CAST2022/CAST/Hardware/M3 Pan Head 6mm.SLDPRT

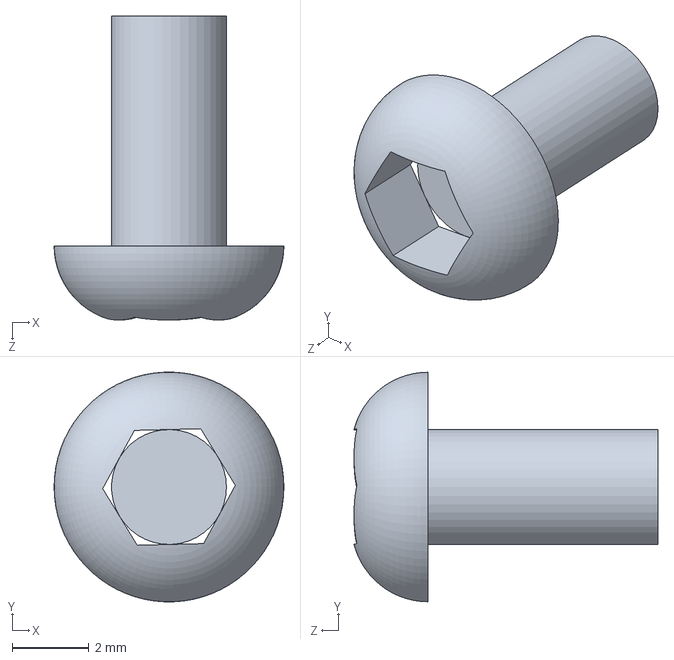
[picture p14: CAD file, 2021-12-28]
Hardware/M3 Pan Head 6mm.SLDPRT
6.00 x 5.99 x 7.94 mm
