CAST2022/CAST/Hardware/SOLIDWORKSComposer/encoderBracketV2.SLDPRT

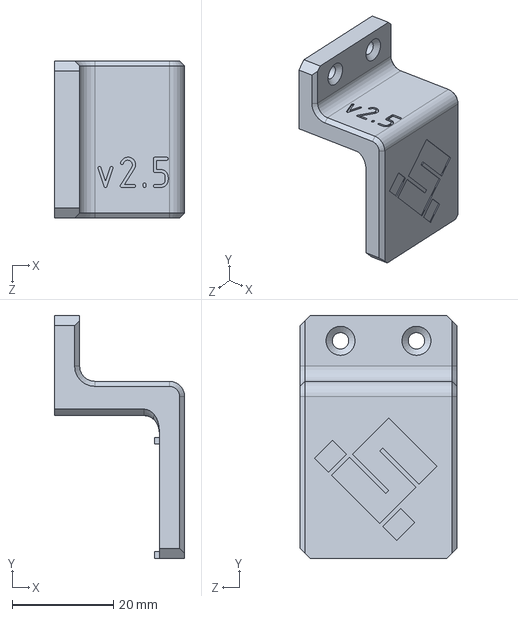
[picture p15: CAD file, 2021-12-27]
Hardware/SOLIDWORKSComposer/encoderBracketV2.SLDPRT
25.8 x 48.0 x 31.0 mm
