CAST2022/CAST/Hardware/SC8LUU Double Bearing Mount.SLDPRT

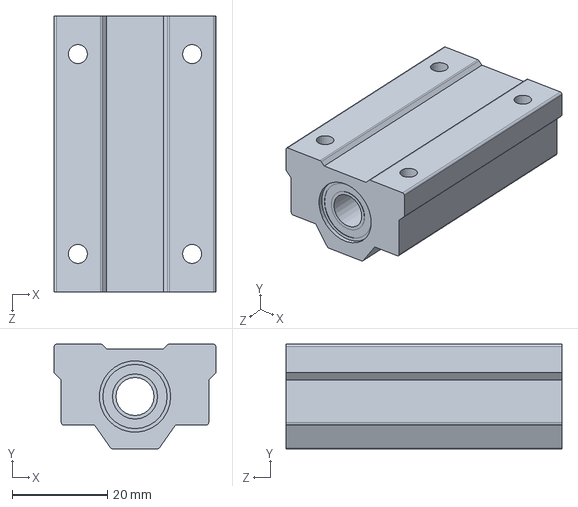
[picture p16: CAD file, 2021-12-28]
Hardware/SC8LUU Double Bearing Mount.SLDPRT
34.0 x 22.0 x 58.0 mm
