CAST2022/CAST/Hardware/SOLIDWORKSComposer/batMount v2.3.SLDPRT

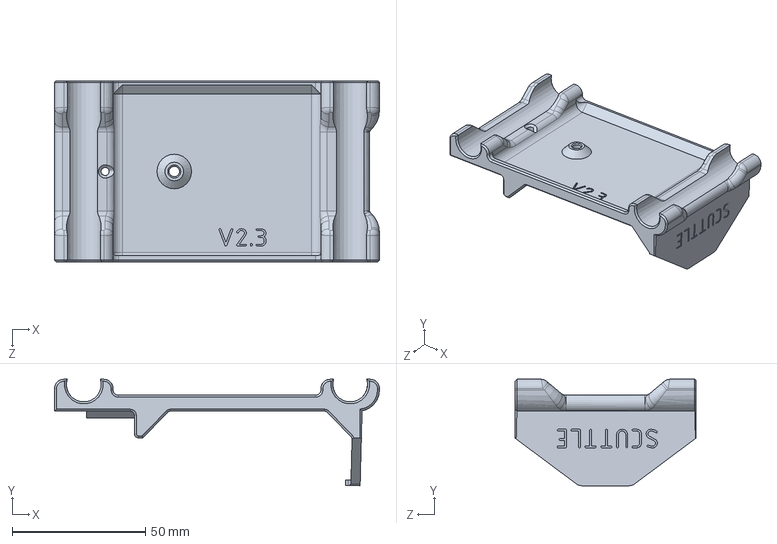
[picture p17: CAD file, 2021-12-27]
Hardware/SOLIDWORKSComposer/batMount v2.3.SLDPRT
122.0 x 40.0 x 68.0 mm
