CAST2022/CAST/Hardware/Nema 17 Mount.SLDPRT

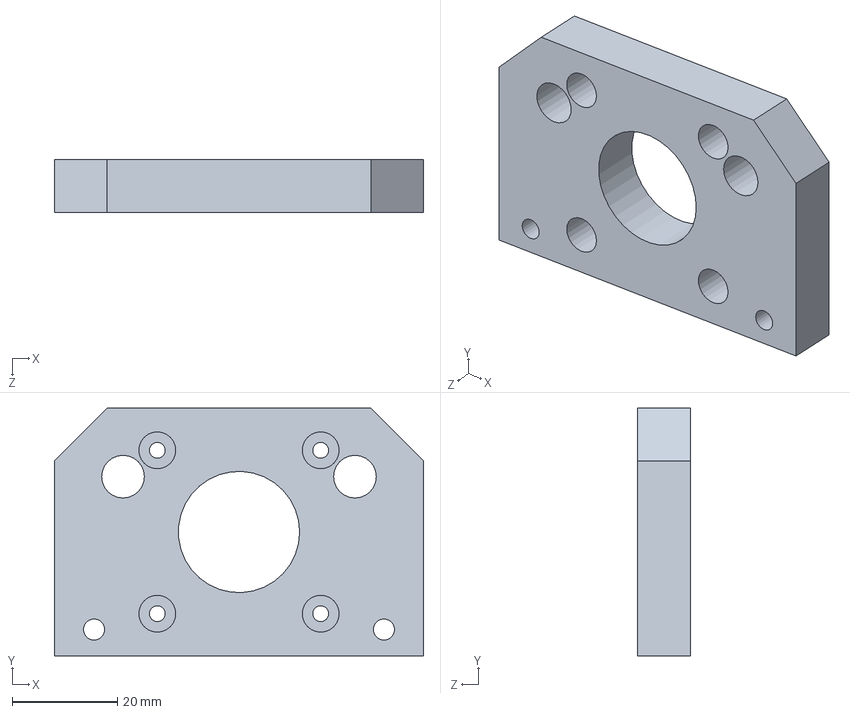
[picture p18: CAD file, 2021-12-28]
Hardware/Nema 17 Mount.SLDPRT
70.0 x 47.0 x 10.0 mm
