CAST2022/CAST/Hardware/SOLIDWORKSComposer/casterCarrier.SLDPRT

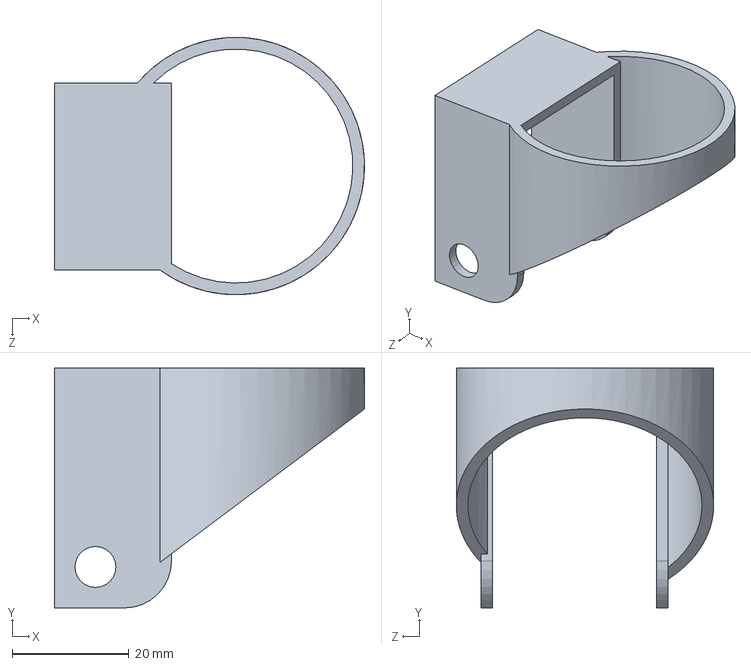
[picture p19: CAD file, 2021-12-27]
Hardware/SOLIDWORKSComposer/casterCarrier.SLDPRT
53.0 x 41.0 x 44.0 mm
