CAST2022/CAST/Hardware/12.17 by 3.54 in cover.SLDPRT

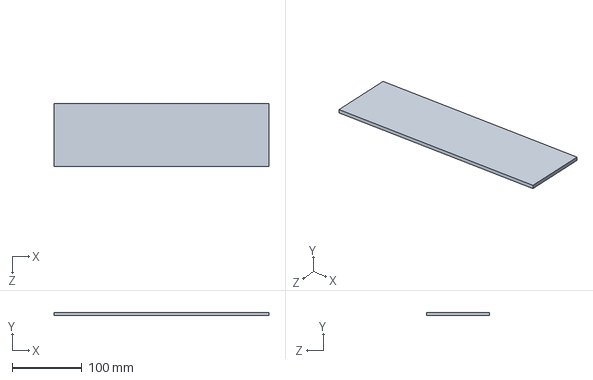
[picture p20: CAD file, 2021-12-28]
Hardware/12.17 by 3.54 in cover.SLDPRT
309.0 x 4.76 x 89.9 mm
