CAST2022/CAST/Hardware/SOLIDWORKSComposer/motor v1.sldprt

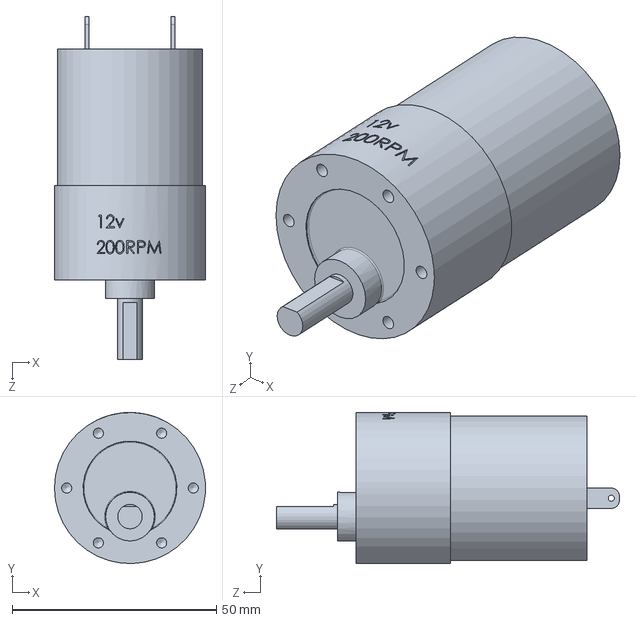
[picture p21: CAD file, 2021-12-27]
Hardware/SOLIDWORKSComposer/motor v1.sldprt
37.0 x 37.0 x 84.0 mm
