CAST2022/CAST/Hardware/SOLIDWORKSComposer/endCap.SLDPRT

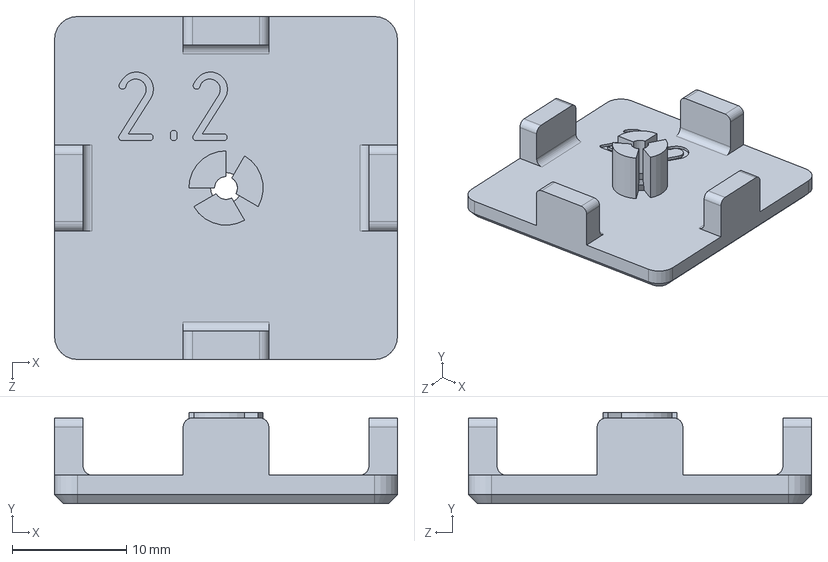
[picture p22: CAD file, 2021-12-27]
Hardware/SOLIDWORKSComposer/endCap.SLDPRT
30.0 x 8.00 x 30.0 mm
