CAST2022/CAST/Hardware/46.31 by 7.28 in cover.SLDPRT

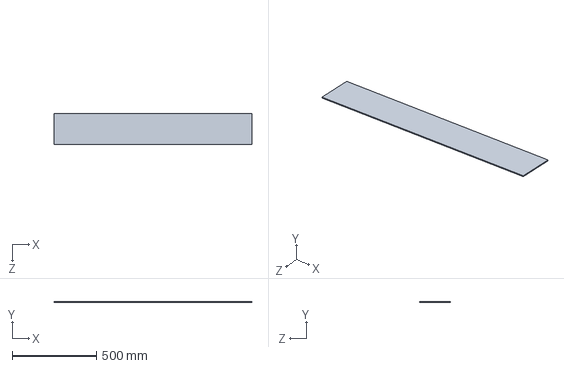
[picture p23: CAD file, 2021-12-28]
Hardware/46.31 by 7.28 in cover.SLDPRT
1176.3 x 4.76 x 184.8 mm
