CAST2022/CAST/Hardware/12.17 by 6 in cover.SLDPRT

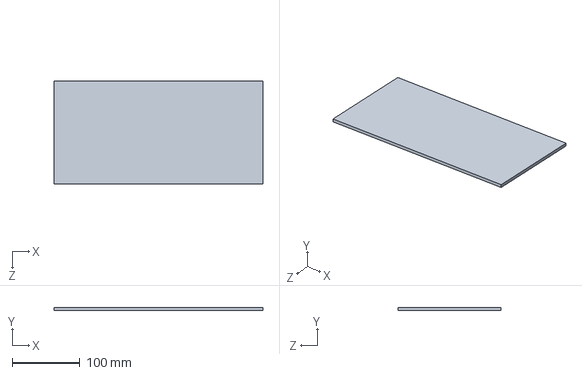
[picture p24: CAD file, 2021-12-28]
Hardware/12.17 by 6 in cover.SLDPRT
309.0 x 4.76 x 152.4 mm
