CAST2022/CAST/Hardware/SOLIDWORKSComposer/BeagleMount V2.SLDPRT

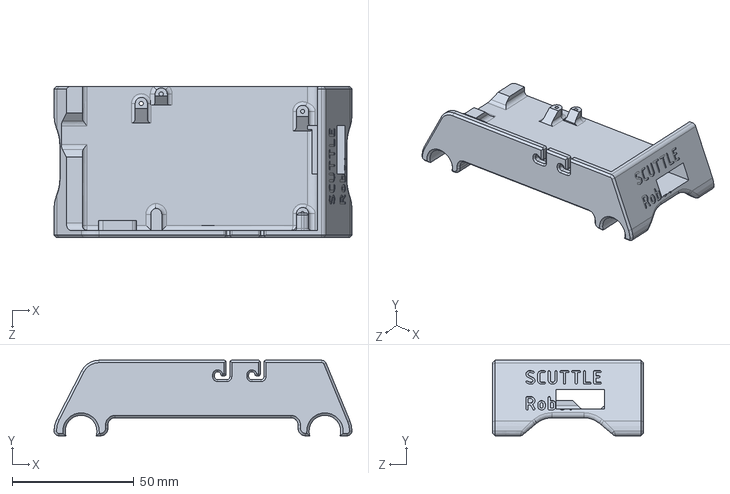
[picture p25: CAD file, 2021-12-27]
Hardware/SOLIDWORKSComposer/BeagleMount V2.SLDPRT
122.2 x 31.0 x 62.0 mm
