CAST2022/CAST/Hardware/RPLiDAR S2.SLDPRT

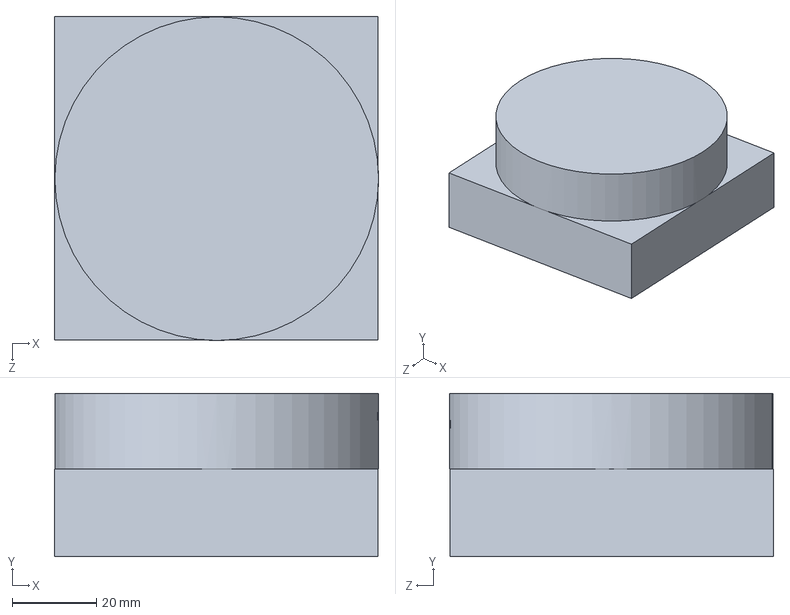
[picture p26: CAD file, 2021-12-28]
Hardware/RPLiDAR S2.SLDPRT
77.1 x 38.8 x 77.1 mm
