CAST2022/CAST/Hardware/SOLIDWORKSComposer/batPCB.SLDPRT

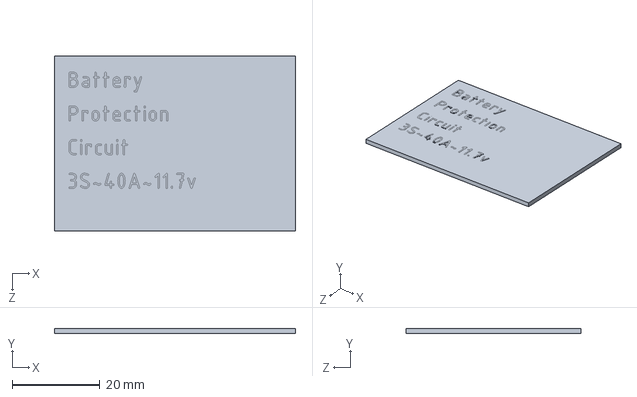
[picture p27: CAD file, 2021-12-27]
Hardware/SOLIDWORKSComposer/batPCB.SLDPRT
55.0 x 1.25 x 40.0 mm
