CAST2022/CAST/Hardware/SOLIDWORKSComposer/batPanel.SLDPRT

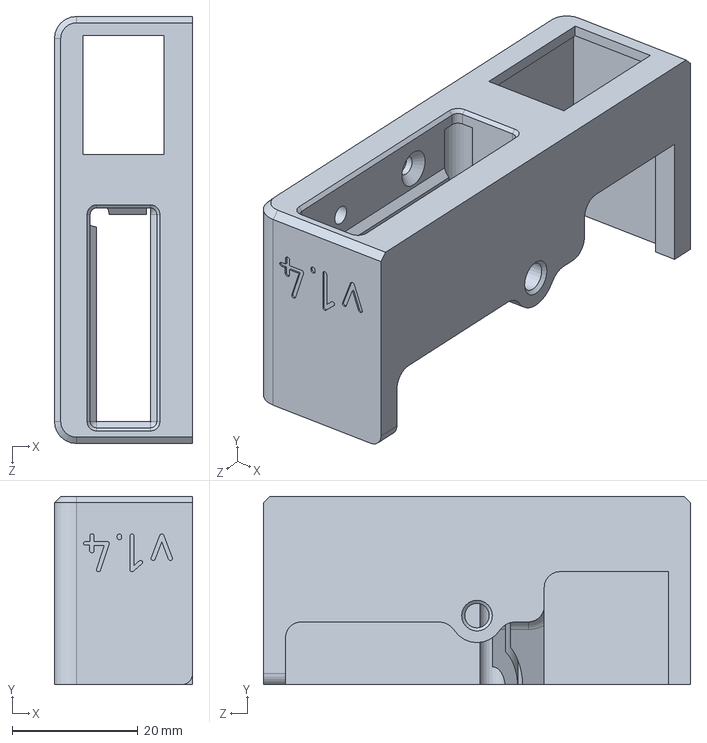
[picture p28: CAD file, 2021-12-27]
Hardware/SOLIDWORKSComposer/batPanel.SLDPRT
22.0 x 30.0 x 68.0 mm
