CAST2022/CAST/Hardware/UV LED PCB.SLDPRT

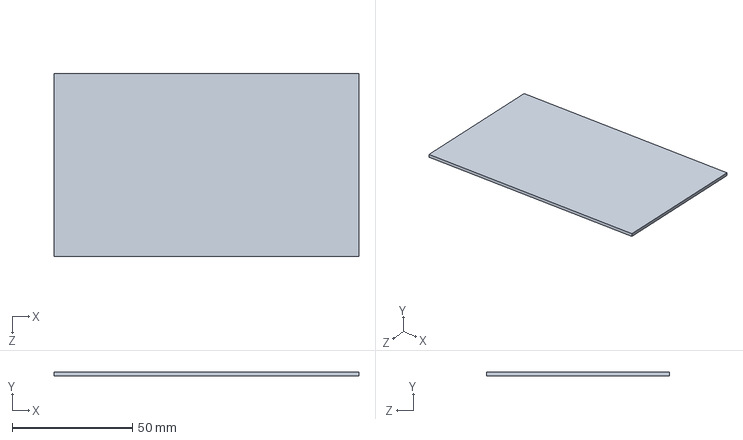
[picture p29: CAD file, 2021-12-28]
Hardware/UV LED PCB.SLDPRT
127.0 x 1.59 x 76.2 mm
