CAST2022/CAST/Hardware/8mm x 721mm Rod.SLDPRT

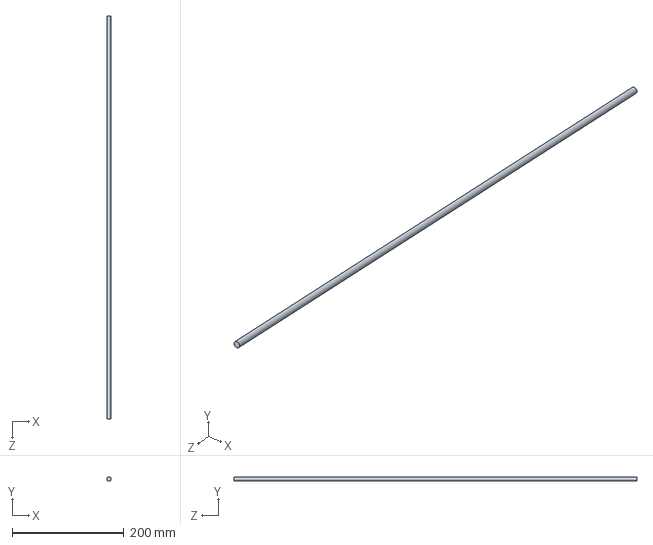
[picture p30: CAD file, 2021-12-28]
Hardware/8mm x 721mm Rod.SLDPRT
8.00 x 8.00 x 721.0 mm
