CAST2022/CAST/Hardware/SOLIDWORKSComposer/casterPlate.SLDPRT

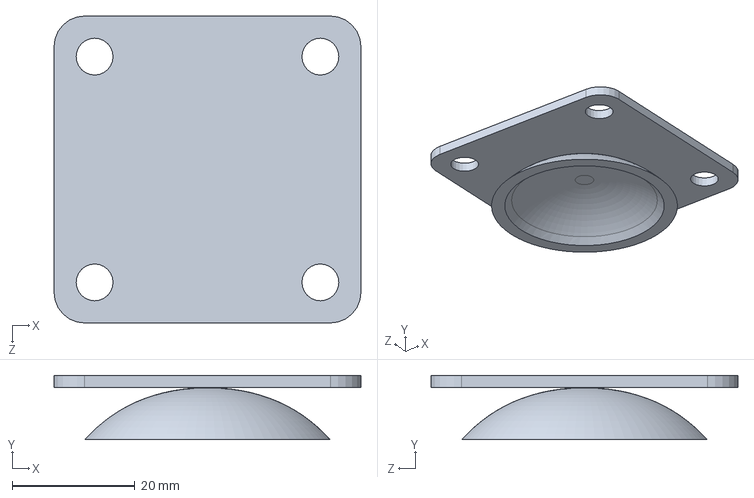
[picture p31: CAD file, 2021-12-27]
Hardware/SOLIDWORKSComposer/casterPlate.SLDPRT
50.0 x 10.5 x 50.0 mm
