CAST2022/CAST/Hardware/SOLIDWORKSComposer/casterWheel.SLDPRT

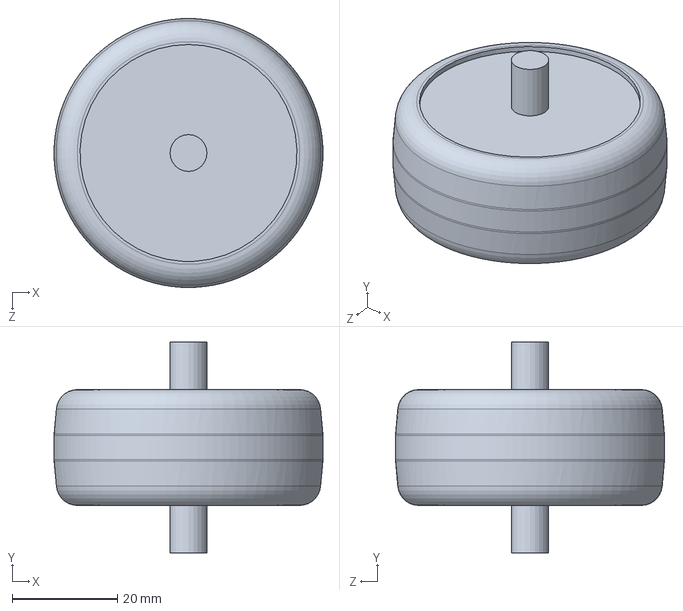
[picture p32: CAD file, 2021-12-27]
Hardware/SOLIDWORKSComposer/casterWheel.SLDPRT
51.1 x 40.0 x 51.1 mm
