CAST2022/CAST/Hardware/37.65 by 7.28 in cover.SLDPRT

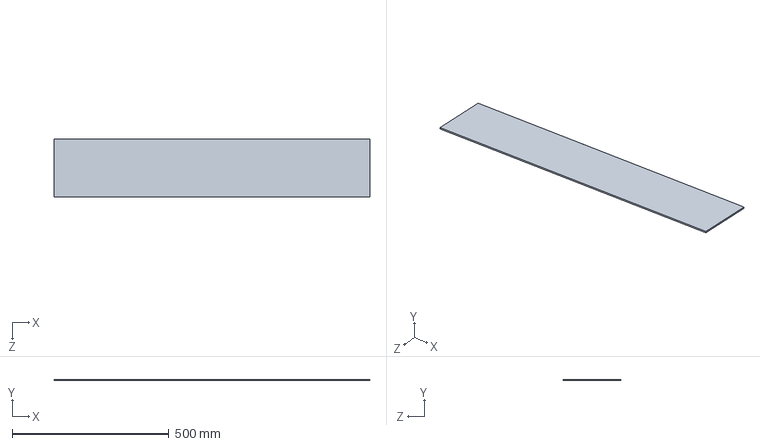
[picture p33: CAD file, 2021-12-28]
Hardware/37.65 by 7.28 in cover.SLDPRT
1007.1 x 4.76 x 184.8 mm
