CAST2022/CAST/Hardware/Plate to support RPLiDAR.SLDPRT

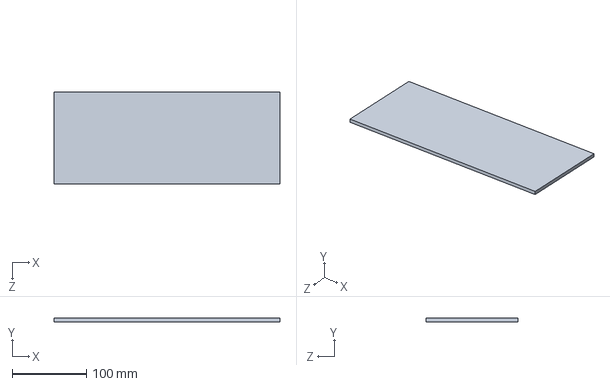
[picture p34: CAD file, 2021-12-28]
Hardware/Plate to support RPLiDAR.SLDPRT
304.8 x 4.76 x 124.0 mm
