CAST2022/CAST/Hardware/SOLIDWORKSComposer/batHoop.SLDPRT

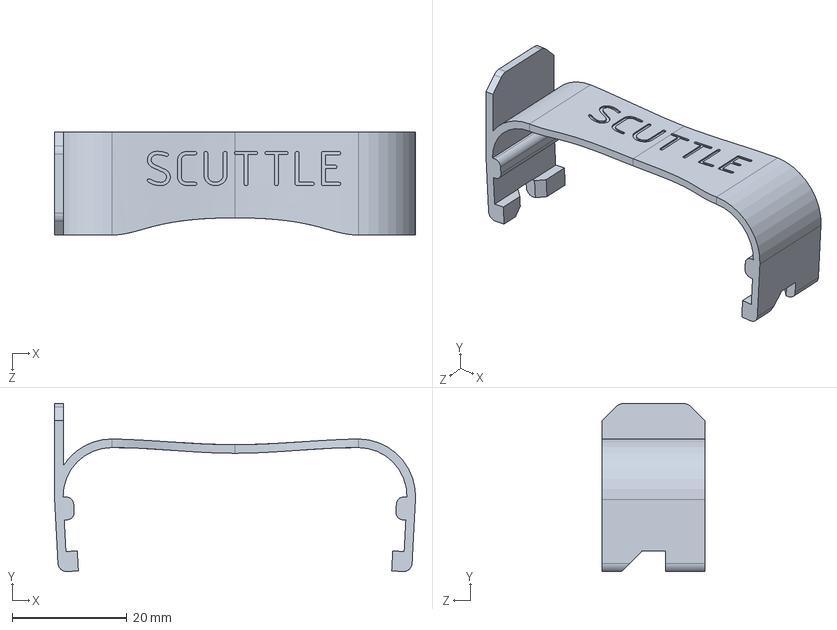
[picture p35: CAD file, 2021-12-27]
Hardware/SOLIDWORKSComposer/batHoop.SLDPRT
63.0 x 29.3 x 18.0 mm
