CAST2022/CAST/Hardware/5 to 8mm x 19mm x 25mm Shaft Coupler.SLDPRT

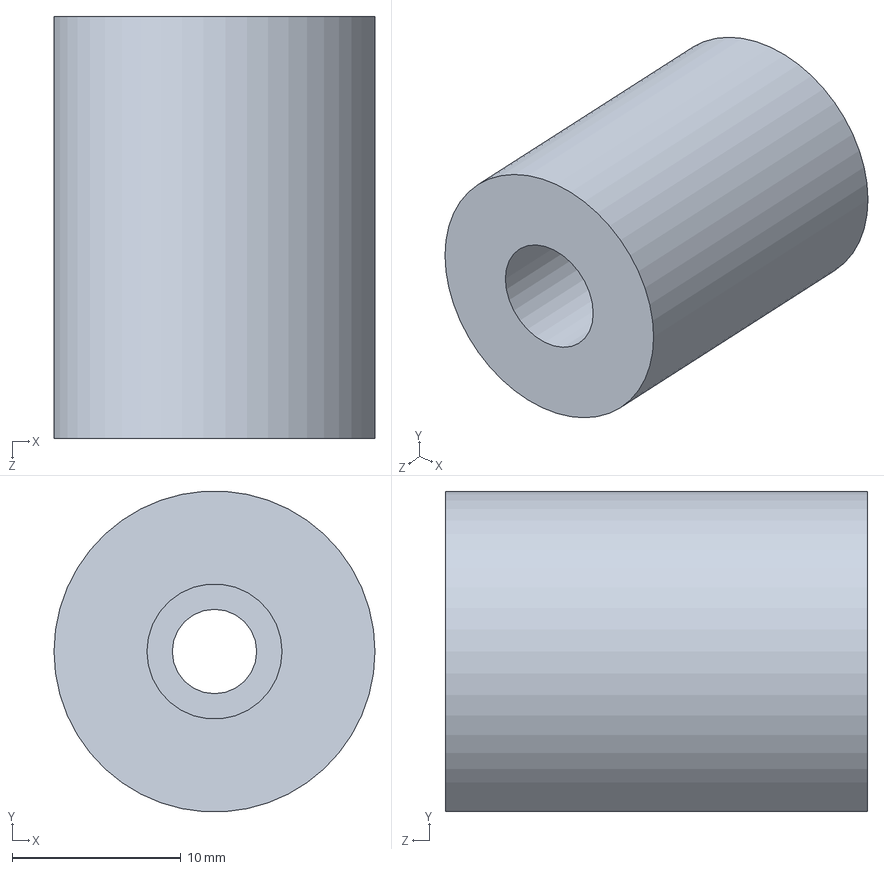
[picture p36: CAD file, 2021-12-28]
Hardware/5 to 8mm x 19mm x 25mm Shaft Coupler.SLDPRT
19.0 x 19.0 x 25.0 mm
