CAST2022/CAST/Hardware/SOLIDWORKSComposer/doveTailF v1.SLDPRT

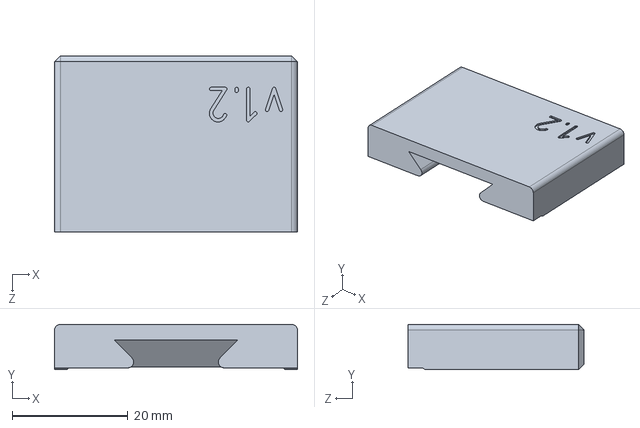
[picture p37: CAD file, 2021-12-27]
Hardware/SOLIDWORKSComposer/doveTailF v1.SLDPRT
42.0 x 7.80 x 30.5 mm
