CAST2022/CAST/Hardware/12 by 3.54 in cover.SLDPRT

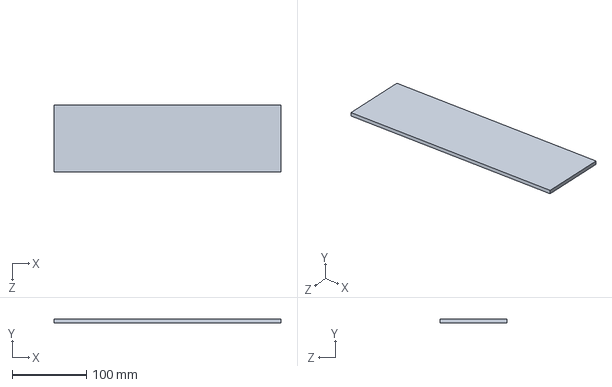
[picture p38: CAD file, 2021-12-28]
Hardware/12 by 3.54 in cover.SLDPRT
304.8 x 4.76 x 89.9 mm
