CAST2022/CAST/Hardware/Nema 17.SLDPRT

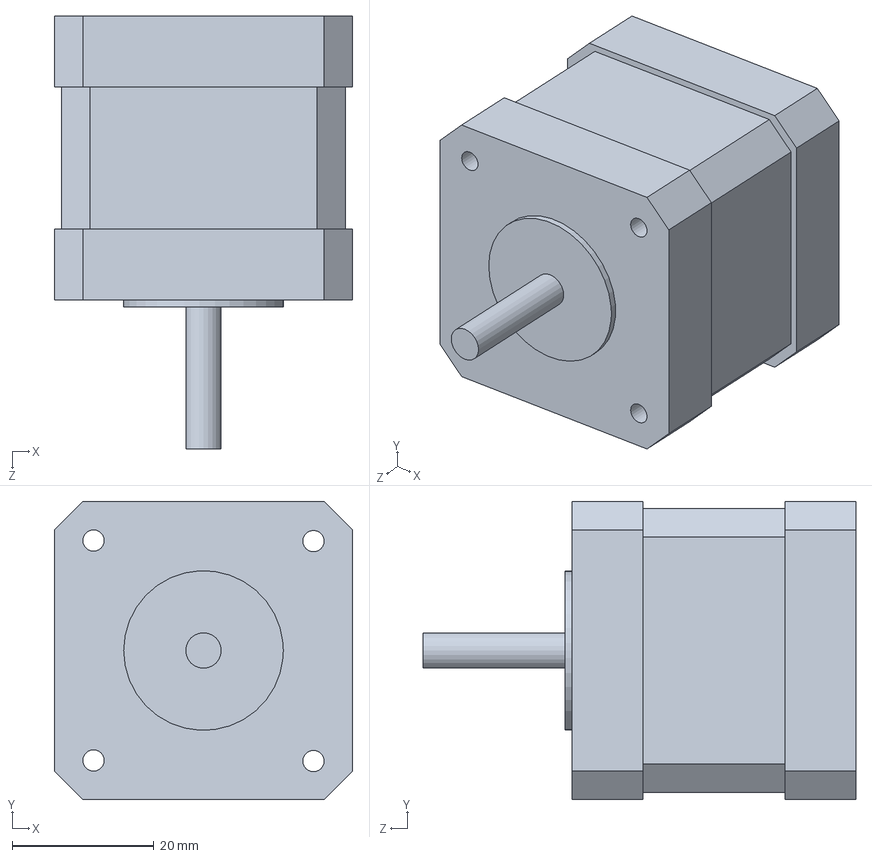
[picture p39: CAD file, 2021-12-28]
Hardware/Nema 17.SLDPRT
42.0 x 42.0 x 61.0 mm
