CAST2022/CAST/Hardware/SOLIDWORKSComposer/motorPulley v2.SLDPRT

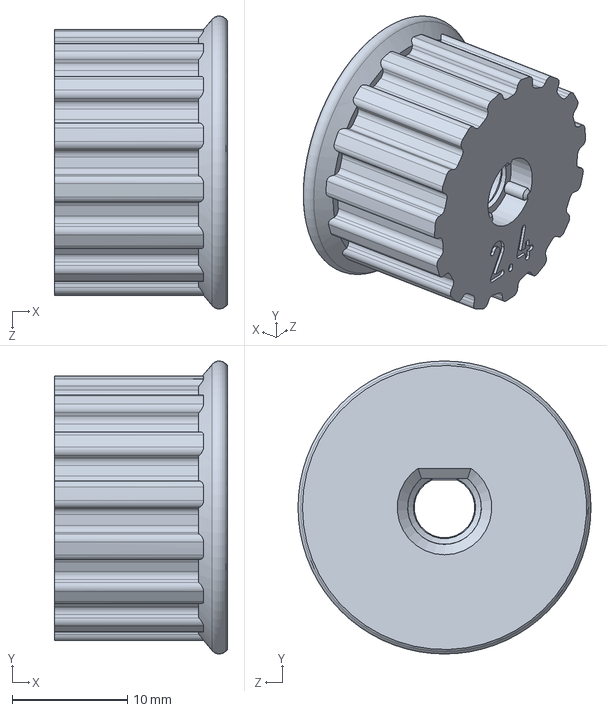
[picture p40: CAD file, 2021-12-27]
Hardware/SOLIDWORKSComposer/motorPulley v2.SLDPRT
15.0 x 25.4 x 25.4 mm
