CAST2022/CAST/Hardware/17.93 by 7.28 in cover.SLDPRT

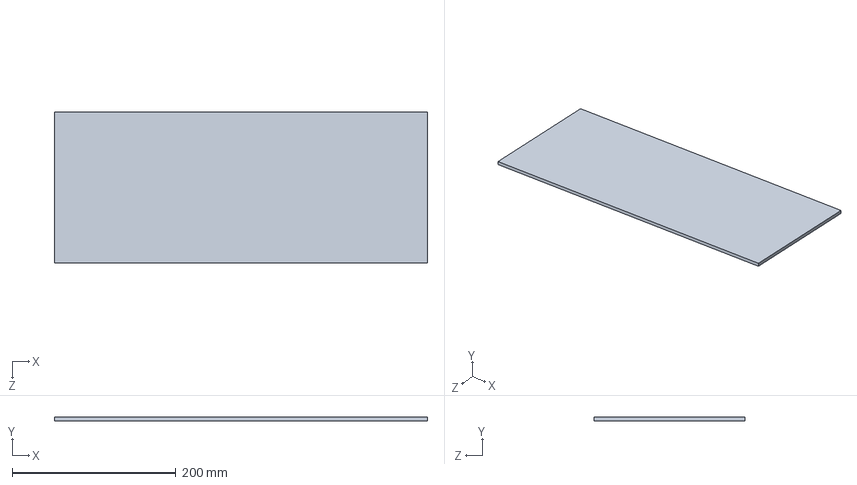
[picture p41: CAD file, 2021-12-28]
Hardware/17.93 by 7.28 in cover.SLDPRT
455.3 x 4.76 x 184.8 mm
