CAST2022/CAST/Hardware/SOLIDWORKSComposer/Ras Pi 3B+.SLDPRT

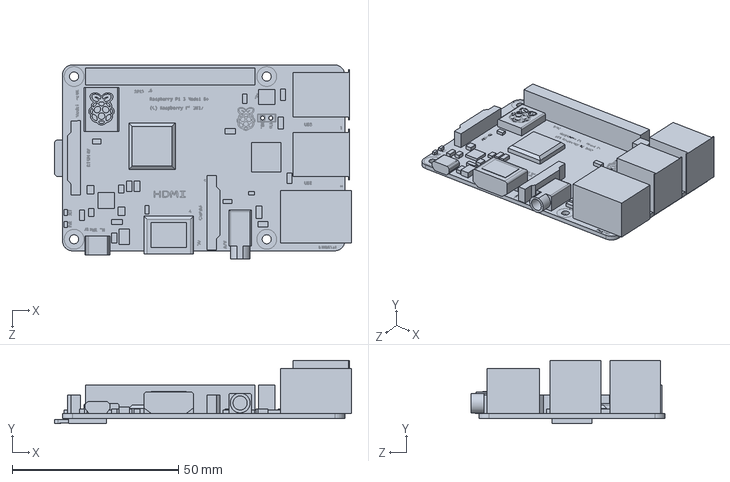
[picture p42: CAD file, 2021-12-27]
Hardware/SOLIDWORKSComposer/Ras Pi 3B+.SLDPRT
89.4 x 19.1 x 58.5 mm
