CAST2022/CAST/Hardware/47.31 by 7.28 in cover.SLDPRT

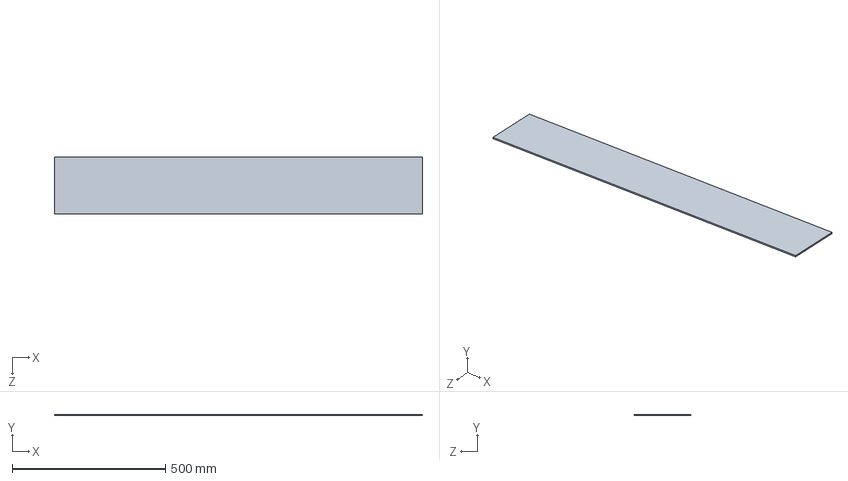
[picture p43: CAD file, 2021-12-28]
Hardware/47.31 by 7.28 in cover.SLDPRT
1201.7 x 4.76 x 184.8 mm
