CAST2022/CAST/Hardware/SOLIDWORKSComposer/batCell.SLDPRT

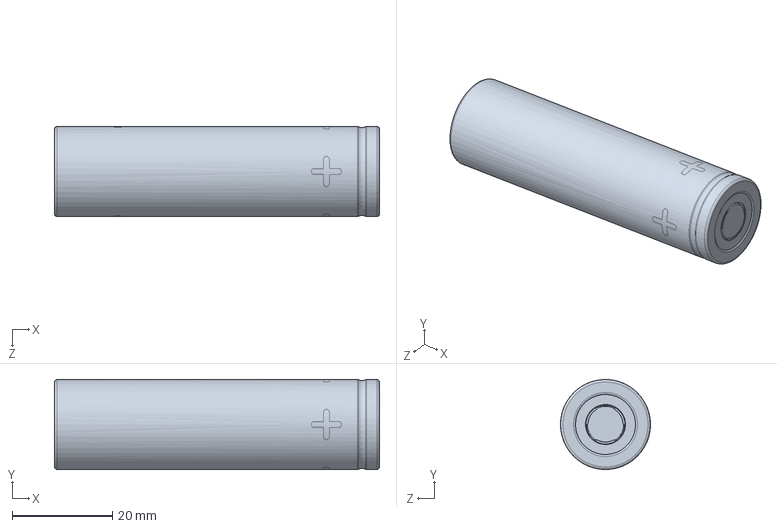
[picture p44: CAD file, 2021-12-27]
Hardware/SOLIDWORKSComposer/batCell.SLDPRT
65.0 x 18.0 x 18.0 mm
