CAST2022/CAST/Hardware/SOLIDWORKSComposer/hBridge.SLDPRT

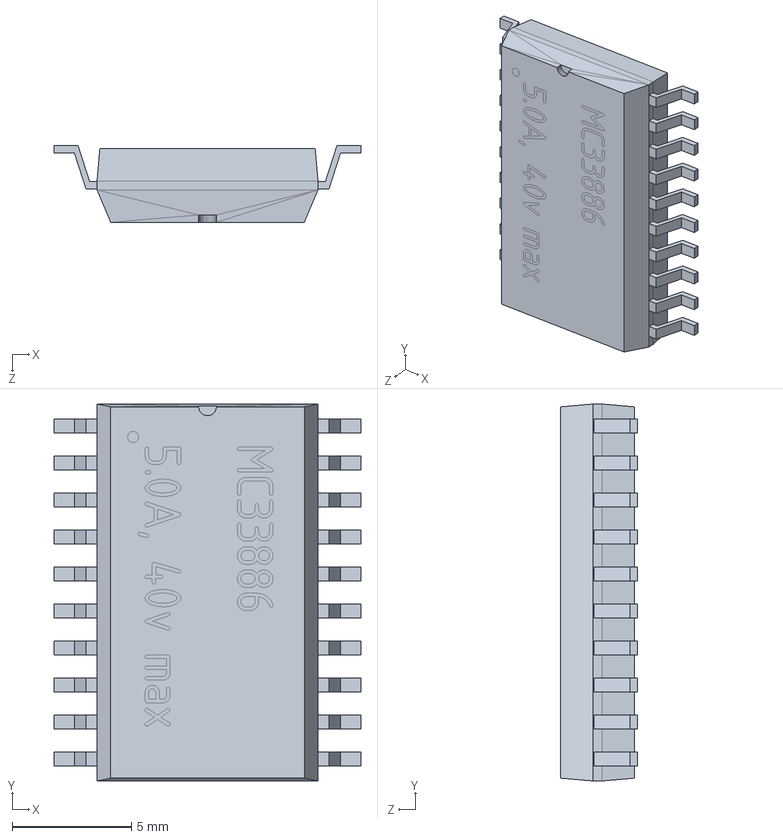
[picture p45: CAD file, 2021-12-27]
Hardware/SOLIDWORKSComposer/hBridge.SLDPRT
12.9 x 15.8 x 3.23 mm
