CAST2022/CAST/Hardware/X5-Export.SLDPRT

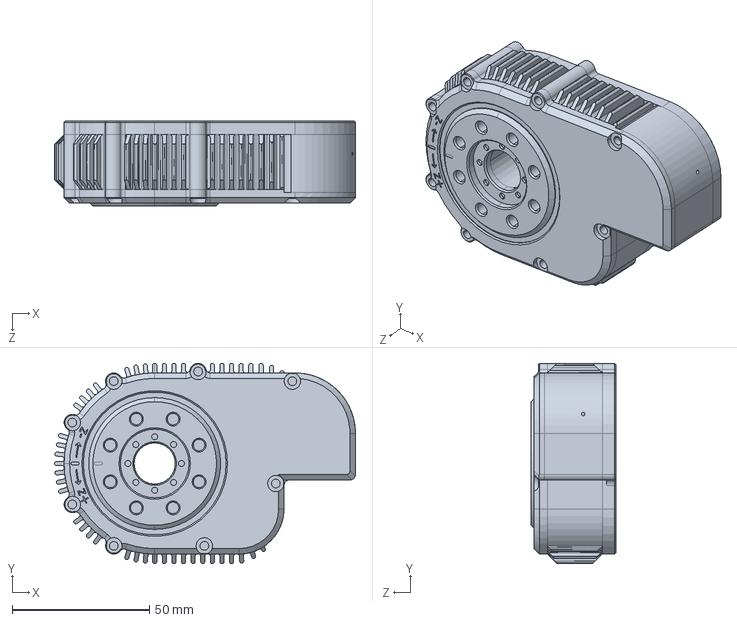
[picture p46: CAD file, 2021-12-28]
Hardware/X5-Export.SLDPRT
109.6 x 73.0 x 31.0 mm
