CAST2022/CAST/Hardware/12 by 6 in cover.SLDPRT

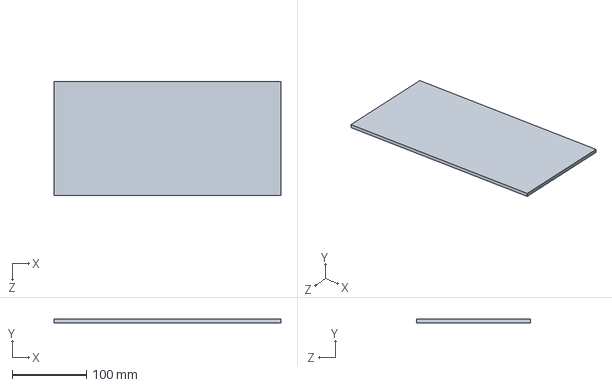
[picture p47: CAD file, 2021-12-28]
Hardware/12 by 6 in cover.SLDPRT
304.8 x 4.76 x 152.4 mm
