CAST2022/CAST/Hardware/SOLIDWORKSComposer/motorPulley HTD5 v3.0.STEP

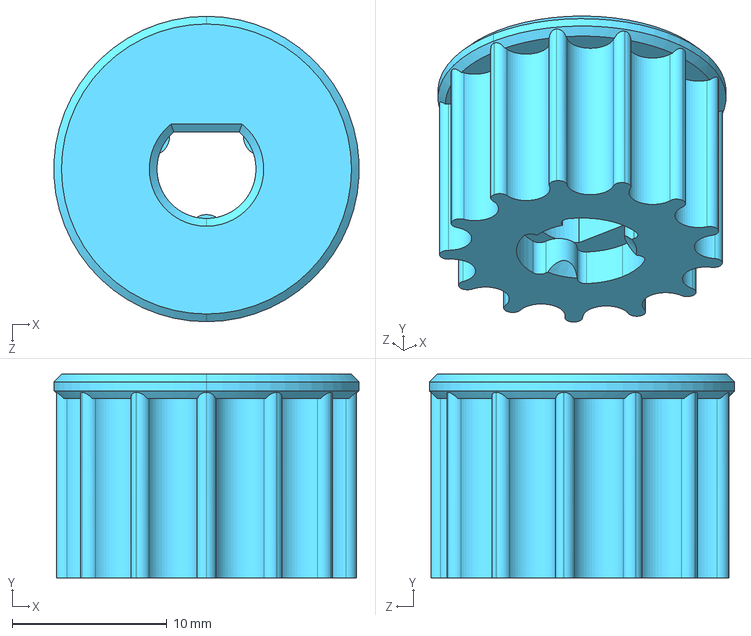
[picture p48: CAD file, 2021-12-27]
Hardware/SOLIDWORKSComposer/motorPulley HTD5 v3.0.STEP
19.7 x 13.2 x 19.7 mm
