CAST2022/CAST/Hardware/8mm x 405mm Rod.SLDPRT

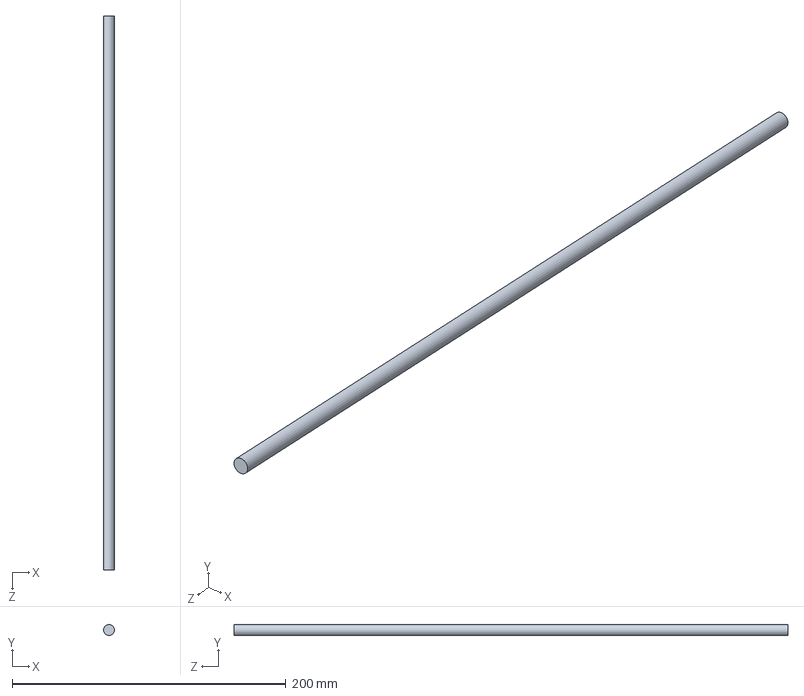
[picture p49: CAD file, 2021-12-28]
Hardware/8mm x 405mm Rod.SLDPRT
8.00 x 8.00 x 405.0 mm
