CAST2022/CAST/Hardware/SOLIDWORKSComposer/pinHeaderDupont.SLDPRT

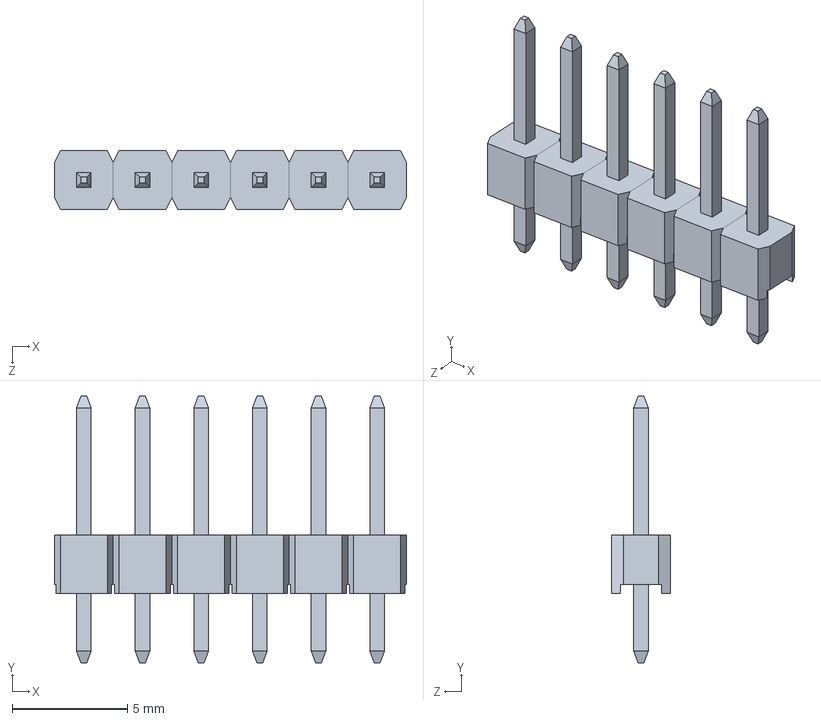
[picture p50: CAD file, 2021-12-27]
Hardware/SOLIDWORKSComposer/pinHeaderDupont.SLDPRT
15.2 x 11.5 x 2.54 mm
