CAST2022/CAST/Hardware/SOLIDWORKSComposer/DualMotorDriverMount.SLDPRT

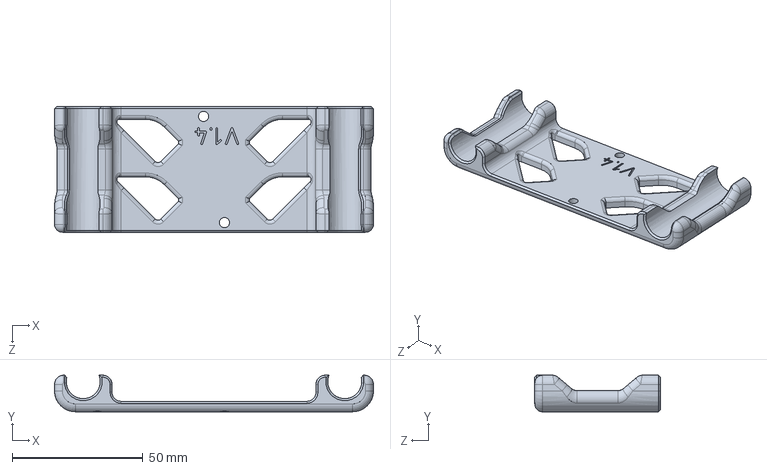
[picture p51: CAD file, 2021-12-27]
Hardware/SOLIDWORKSComposer/DualMotorDriverMount.SLDPRT
122.0 x 14.0 x 48.0 mm
