CAST2022/CAST/Hardware/19.93 by 7.28 in cover.SLDPRT

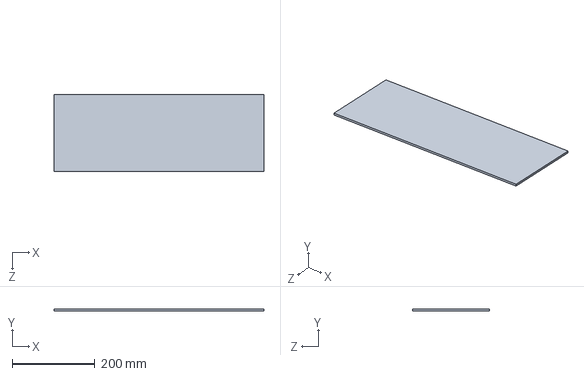
[picture p52: CAD file, 2021-12-28]
Hardware/19.93 by 7.28 in cover.SLDPRT
506.1 x 4.76 x 184.8 mm
