CAST2022/CAST/Hardware/SOLIDWORKSComposer/bracket30mm.SLDPRT

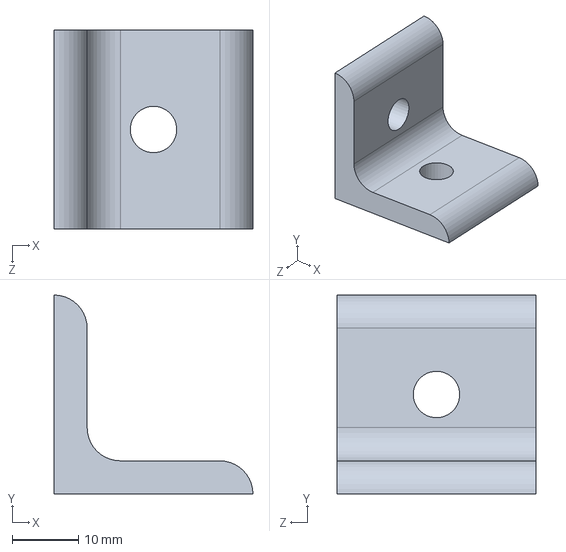
[picture p53: CAD file, 2021-12-27]
Hardware/SOLIDWORKSComposer/bracket30mm.SLDPRT
30.0 x 30.0 x 30.0 mm
