CAST2022/CAST/Hardware/SOLIDWORKSComposer/MotorDriverHW321.SLDPRT

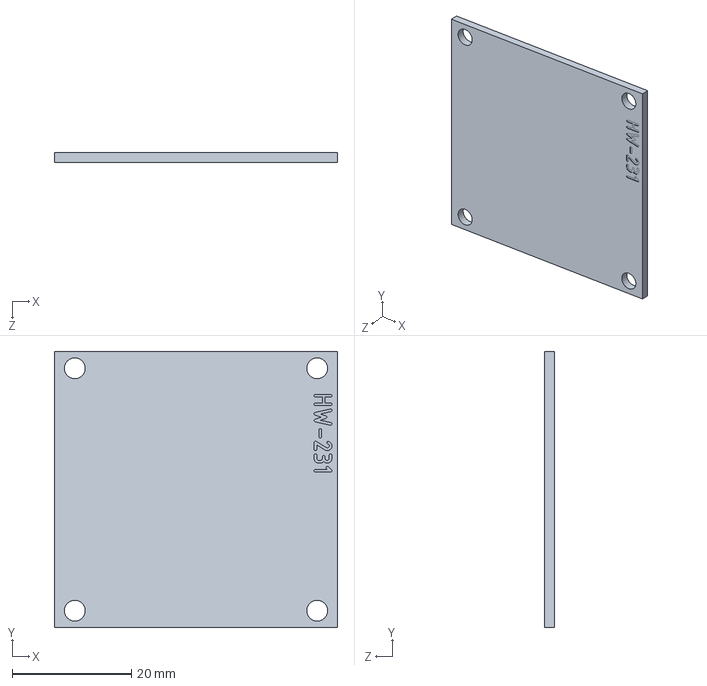
[picture p54: CAD file, 2021-12-27]
Hardware/SOLIDWORKSComposer/MotorDriverHW321.SLDPRT
47.4 x 46.3 x 1.60 mm
