CAST2022/CAST/Hardware/SOLIDWORKSComposer/belt 5M245.SLDPRT

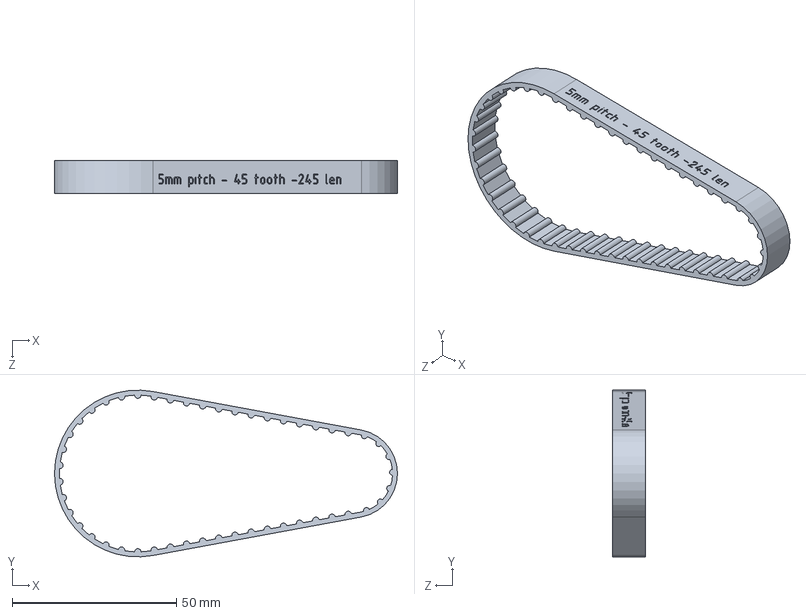
[picture p55: CAD file, 2021-12-27]
Hardware/SOLIDWORKSComposer/belt 5M245.SLDPRT
104.3 x 50.7 x 10.0 mm
