CAST2022/CAST/Hardware/SOLIDWORKSComposer/rodBracket v4.SLDPRT

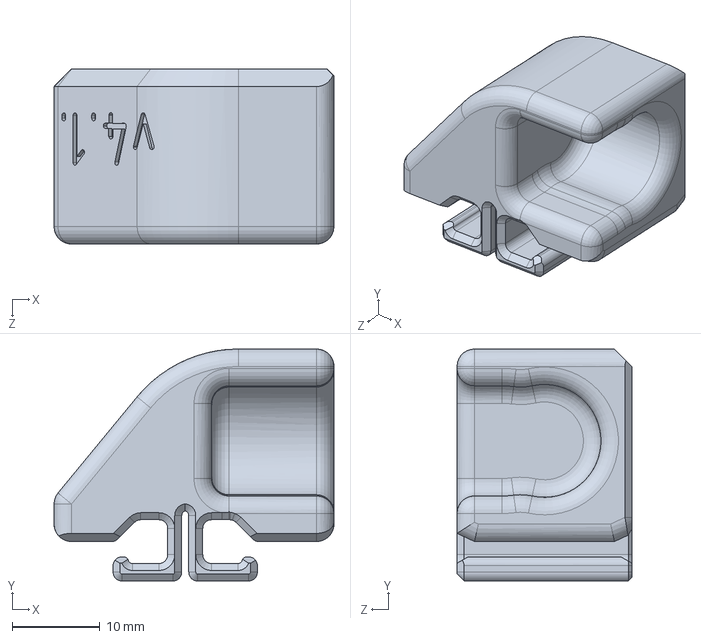
[picture p56: CAD file, 2021-12-27]
Hardware/SOLIDWORKSComposer/rodBracket v4.SLDPRT
32.0 x 26.5 x 20.0 mm
