CAST2022/CAST/Hardware/SOLIDWORKSComposer/encoder.SLDPRT

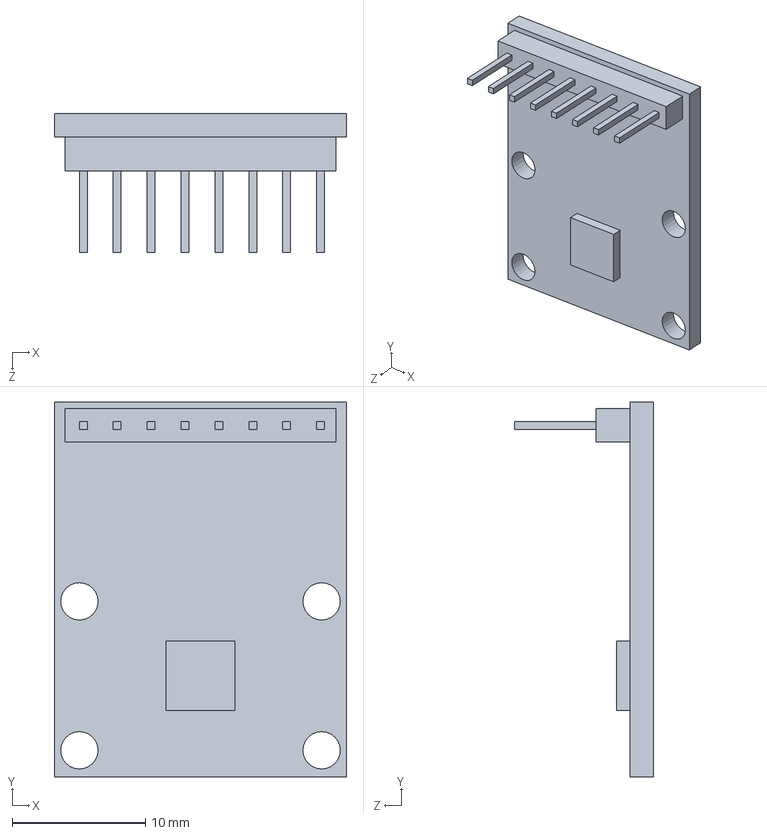
[picture p57: CAD file, 2021-12-27]
Hardware/SOLIDWORKSComposer/encoder.SLDPRT
21.9 x 28.1 x 10.4 mm
