CAST2022/CAST/Hardware/SOLIDWORKSComposer/i2cBracket v2.SLDPRT

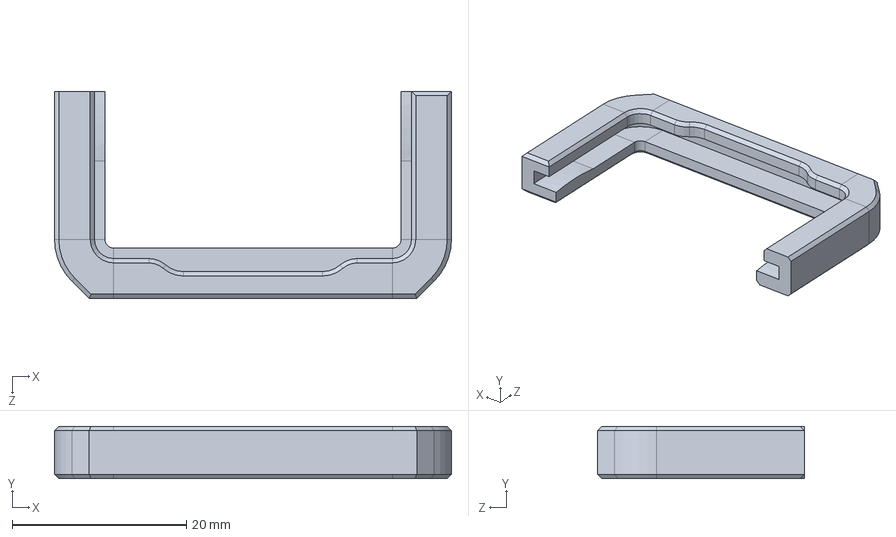
[picture p58: CAD file, 2021-12-27]
Hardware/SOLIDWORKSComposer/i2cBracket v2.SLDPRT
45.6 x 6.00 x 23.8 mm
