CAST2022/CAST/Hardware/SOLIDWORKSComposer/pinHeader1x6.SLDPRT

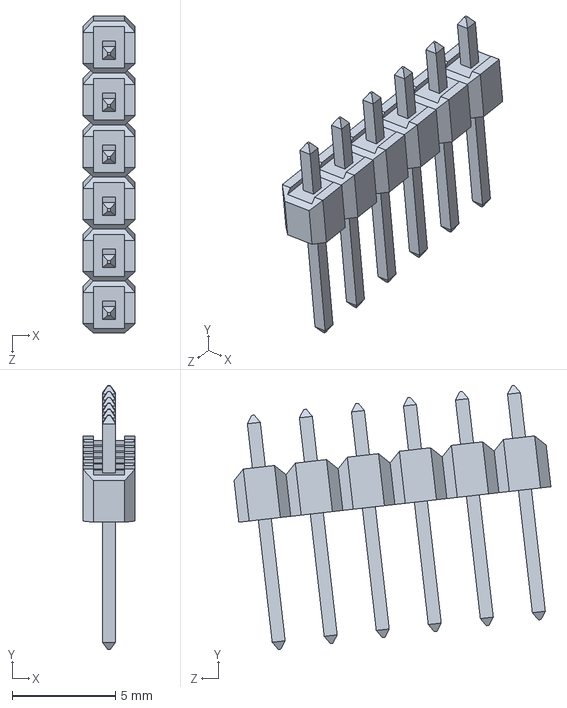
[picture p59: CAD file, 2021-12-27]
Hardware/SOLIDWORKSComposer/pinHeader1x6.SLDPRT
2.54 x 12.8 x 15.4 mm
