CAST2022/CAST/Hardware/SOLIDWORKSComposer/ballBearing608 v1.SLDPRT

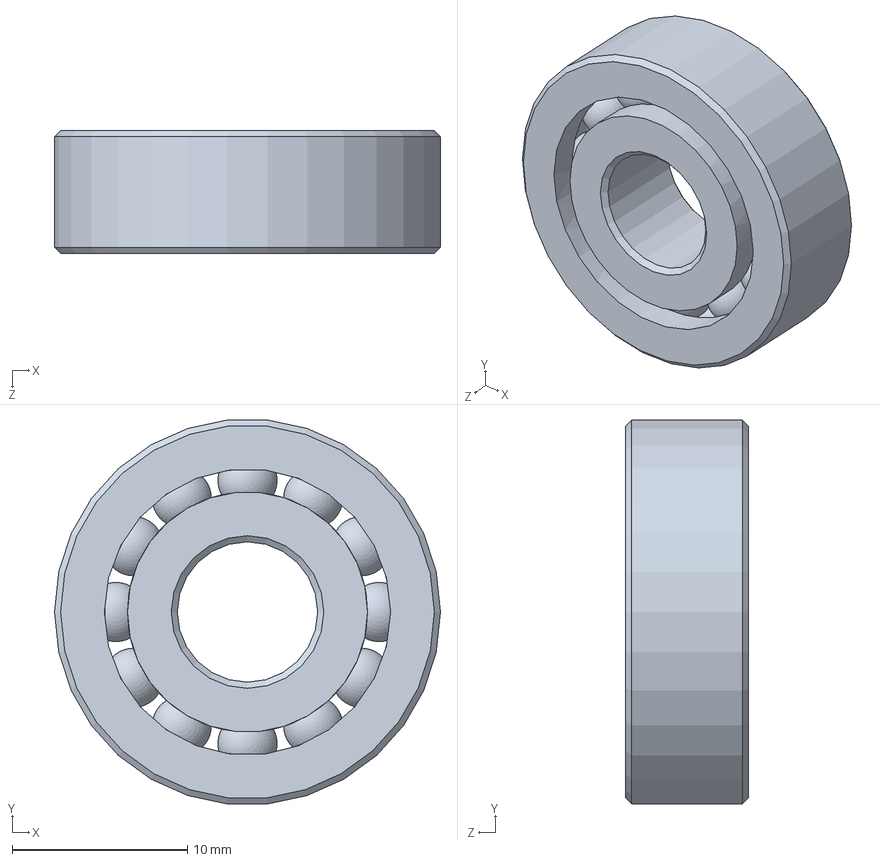
[picture p60: CAD file, 2021-12-27]
Hardware/SOLIDWORKSComposer/ballBearing608 v1.SLDPRT
22.0 x 21.9 x 7.00 mm
