CAST2022/CAST/Hardware/SOLIDWORKSComposer/insertM2.5x3.4.SLDPRT

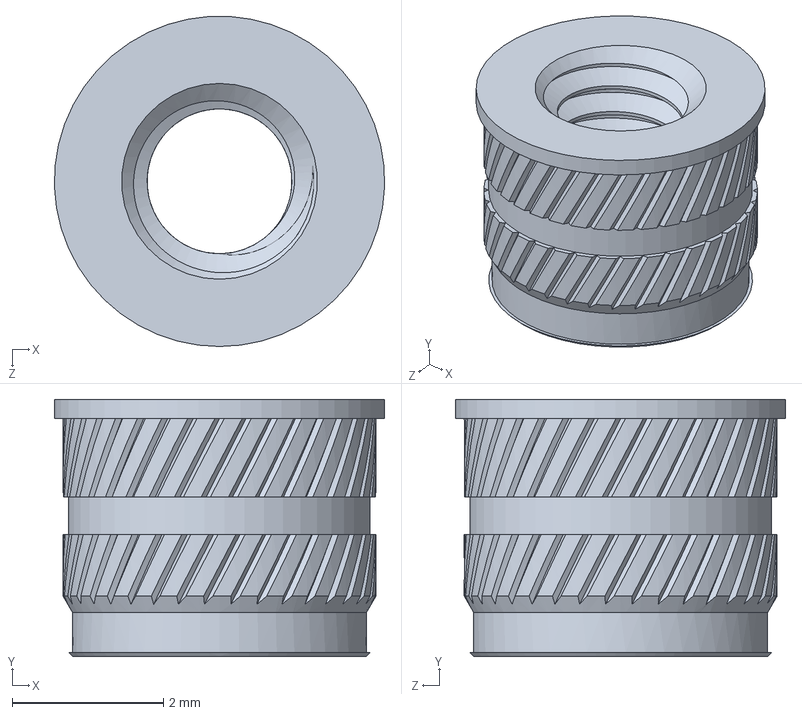
[picture p61: CAD file, 2021-12-27]
Hardware/SOLIDWORKSComposer/insertM2.5x3.4.SLDPRT
4.37 x 3.40 x 4.37 mm
