CAST2022/CAST/Hardware/SOLIDWORKSComposer/batTray.SLDPRT

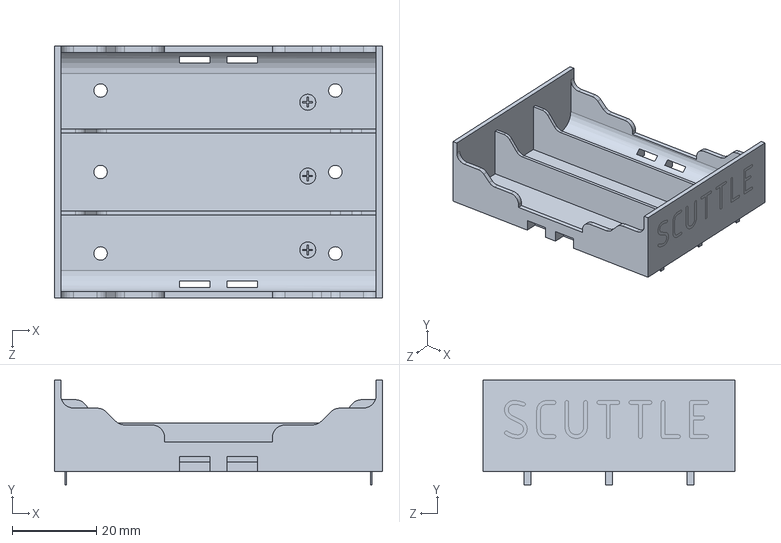
[picture p62: CAD file, 2021-12-27]
Hardware/SOLIDWORKSComposer/batTray.SLDPRT
77.7 x 24.8 x 59.7 mm
