CAST2022/CAST/Hardware/SOLIDWORKSComposer/circuitBoardi2c v1.SLDPRT

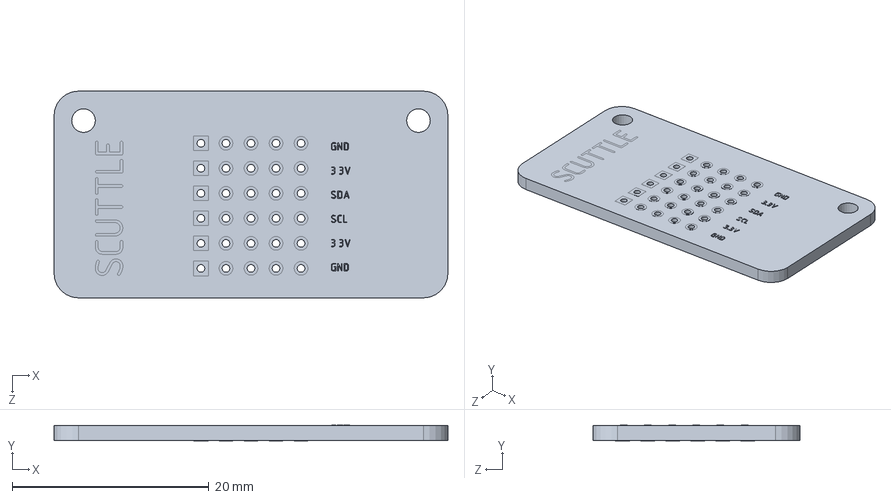
[picture p63: CAD file, 2021-12-27]
Hardware/SOLIDWORKSComposer/circuitBoardi2c v1.SLDPRT
40.0 x 1.60 x 21.0 mm
